LayanJethwa/graphical-calculator/documents/Media/Graph display.jpeg

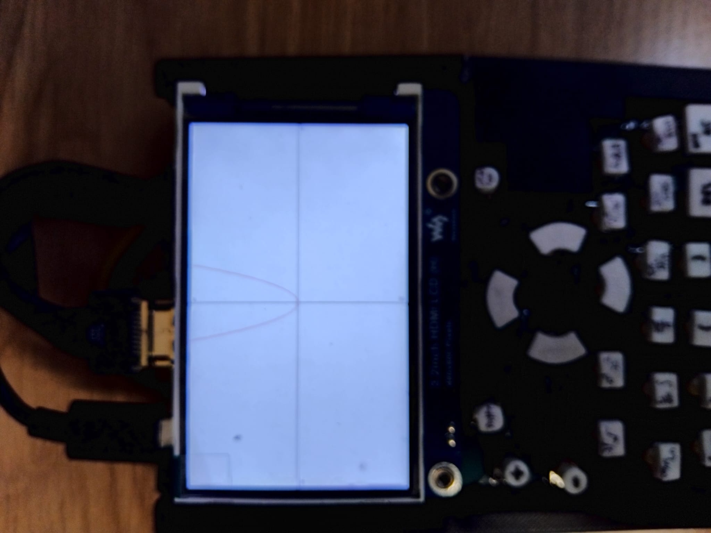
documents/Media/Graph display.jpeg
