LayanJethwa/graphical-calculator/documents/Media/Input display.jpeg

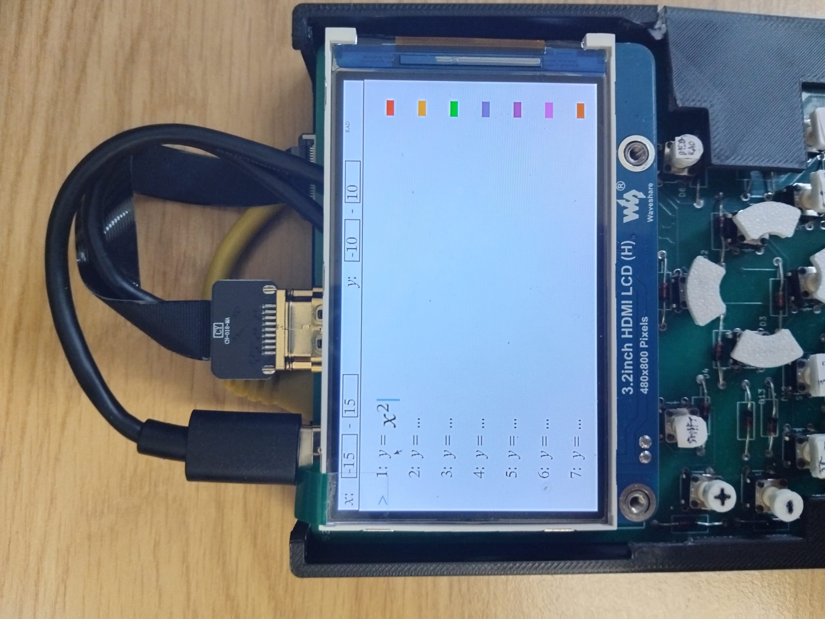
documents/Media/Input display.jpeg
