LayanJethwa/graphical-calculator/hardware/cad/to print/small-0.2.step

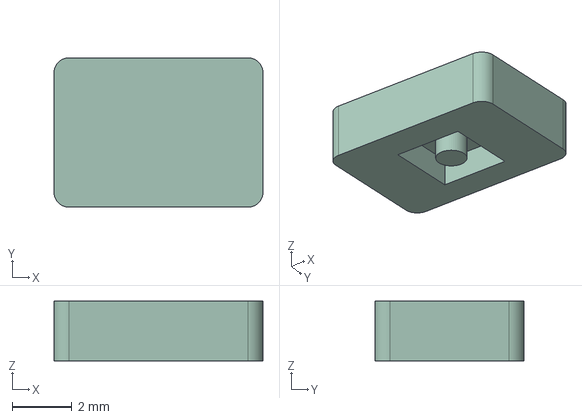
[picture p40: CAD file, 2026-02-20]
hardware/cad/to print/small-0.2.step
7.00 x 5.00 x 2.00 mm
