LayanJethwa/graphical-calculator/hardware/cad/to print/case-top-plate-large-holes.step

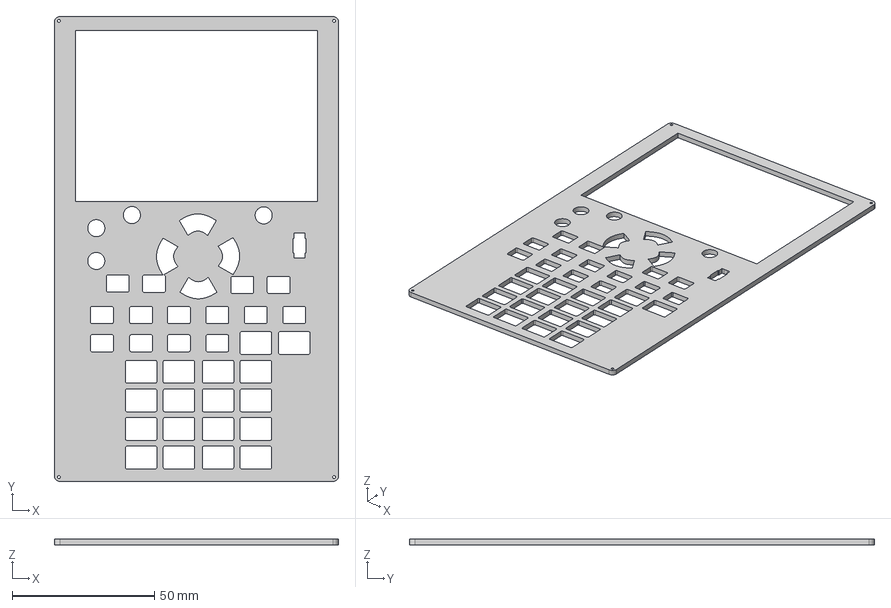
[picture p41: CAD file, 2026-02-20]
hardware/cad/to print/case-top-plate-large-holes.step
99.8 x 163.2 x 2.00 mm
