LayanJethwa/graphical-calculator/hardware/cad/to print/case-base.step

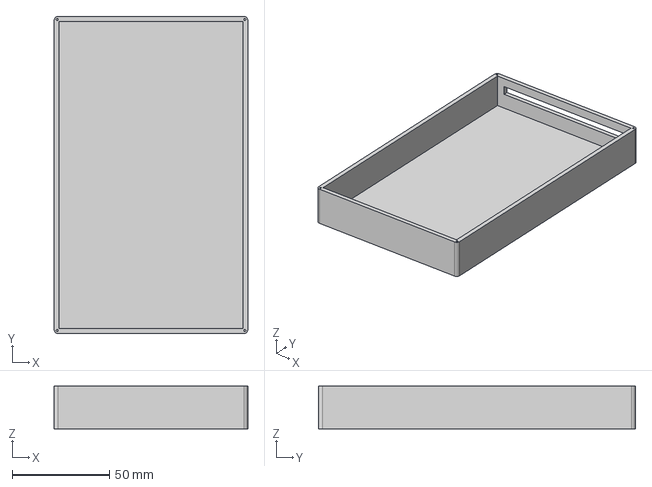
[picture p42: CAD file, 2026-02-20]
hardware/cad/to print/case-base.step
99.8 x 163.2 x 22.0 mm
